Yuna-Miyazaki/bootcamp-ym/cadwork/whoileOrigin.FCStd

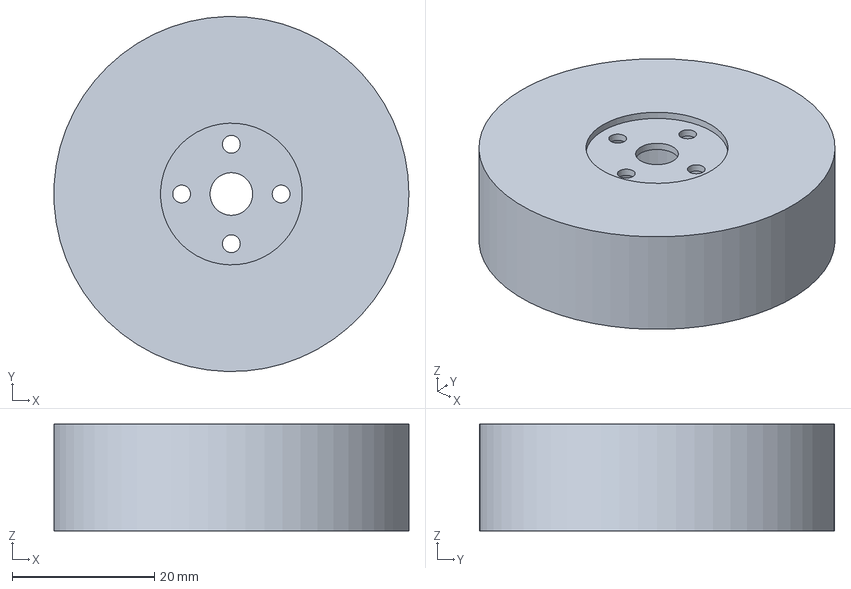
[picture p14: CAD file, 2026-05-18]
cadwork/whoileOrigin.FCStd
50.0 x 50.0 x 15.0 mm
