Yuna-Miyazaki/bootcamp-ym/cadwork/testcat.FCStd

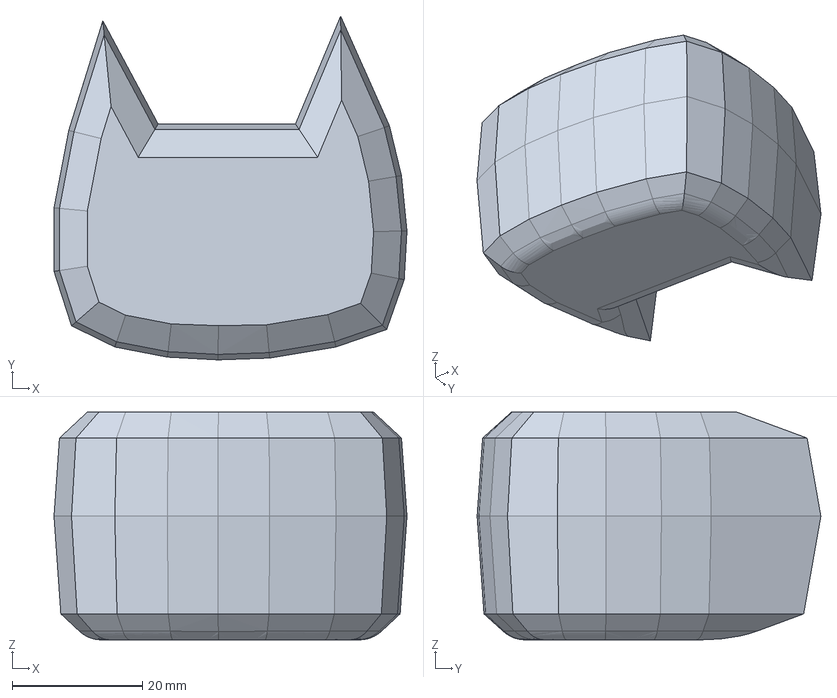
[picture p15: CAD file, 2026-05-18]
cadwork/testcat.FCStd
54.2 x 52.8 x 35.0 mm
