Yuna-Miyazaki/bootcamp-ym/cadwork/ホイール例.FCStd

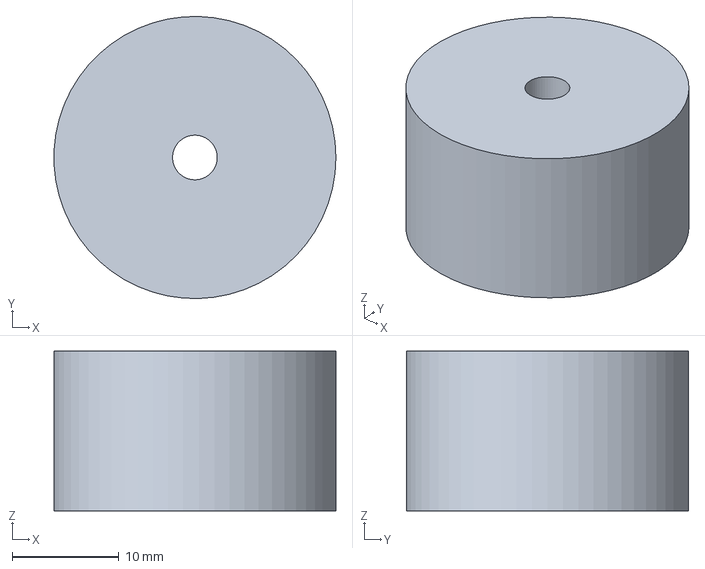
[picture p16: CAD file, 2026-05-18]
cadwork/ホイール例.FCStd
26.4 x 26.4 x 15.0 mm
