Yuna-Miyazaki/bootcamp-ym/cadwork/Neko_Under_front.3mf

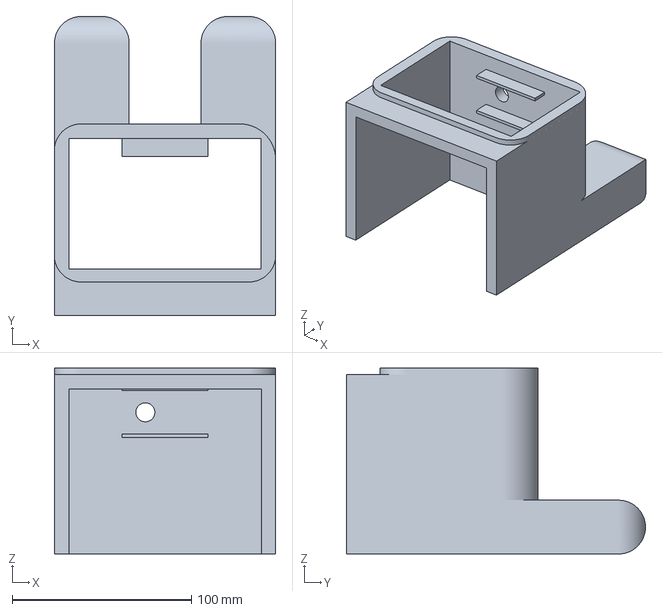
[picture p17: CAD file, 2026-05-18]
cadwork/Neko_Under_front.3mf
123.5 x 166.7 x 103.7 mm
