Yuna-Miyazaki/bootcamp-ym/cadwork/Neko_Head.3mf

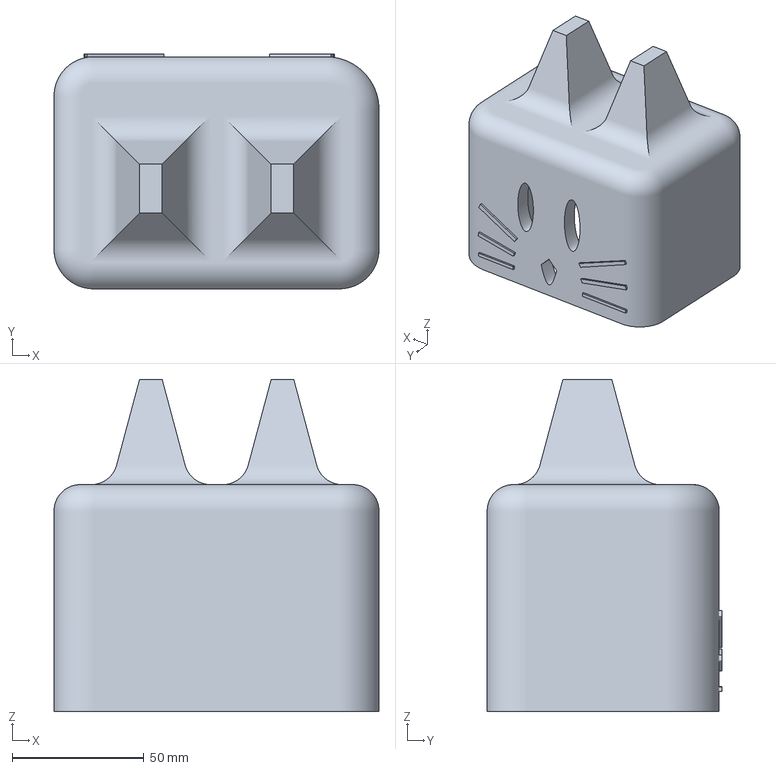
[picture p18: CAD file, 2026-05-18]
cadwork/Neko_Head.3mf
123.5 x 89.1 x 126.3 mm
